Casih/Fluorometer/Fluorometer/ODD.ino

void ODD(){
  //Serial.println("OD");
  digitalWrite(BL, LOW);
  digitalWrite(RL, LOW);
  digitalWrite(GL, LOW); 
  digitalWrite(ODL, HIGH);    //Turn On red led
  digitalWrite(A2, HIGH);
  digitalWrite(A3, LOW);
  lcd.clear();
  lcd.setCursor(0,0);
  lcd.print("WARMING UP...");
  delay(3000);
  lcd.setCursor(0,1);
  lcd.print(char(255));
  delay(18000);
  lcd.setCursor(1,1);
  lcd.print(char(255));
  delay(18000);
  lcd.setCursor(2,1);
  lcd.print(char(255));
  delay(18000);
  lcd.setCursor(3,1);
  lcd.print(char(255));
  delay(18000);
  lcd.setCursor(4,1);
  lcd.print(char(255));
  delay(18000);
  lcd.setCursor(5,1);
  lcd.print(char(255));
  delay(18000);
  lcd.setCursor(6,1);
  lcd.print(char(255));
  delay(18000);
  lcd.setCursor(7,1);
  lcd.print(char(255));
  delay(18000);
  lcd.setCursor(8,1);
  lcd.print(char(255));
  delay(18000);
  lcd.setCursor(9,1);
  lcd.print(char(255));
  delay(18000);
  lcd.setCursor(10,1);
  lcd.print(char(255));
  delay(18000);
  lcd.setCursor(11,1);
  lcd.print(char(255));
  delay(18000);
  lcd.setCursor(12,1);
  lcd.print(char(255));
  delay(18000);
  lcd.setCursor(13,1);
  lcd.print(char(255));
  delay(18000);
  lcd.setCursor(14,1);
  lcd.print(char(255));
  delay(18000);
  lcd.setCursor(15,1);
  lcd.print(char(255));
  delay(18000);
  lcd.clear();
  lcd.setCursor(0,0);
  lcd.print("Modo OD:");
  lcd.setCursor(0,1);
  lcd.print("Enter Blank ");
  lcd.write(7);
  delay(100);
  ModoEn = digitalRead(Enter);
  while (ModoEn == HIGH){     
    ModoEn = digitalRead(Enter);        //waiting for enter
    }
  GetBlank();
  lcd.clear();
  lcd.setCursor(0,0);
  lcd.print("Insert sample");
  lcd.setCursor(0,1);
  lcd.print("....");
  lcd.blink();
  GetOD();     
  Color=4;
  Modo=2;
}
